LegacyNsfw/52Can/Software/Constants.h

// Color definitions
#define BLACK    0x0000
#define BLUE     0x001F
#define RED      0xF800
#define GREEN    0x07E0
#define CYAN     0x07FF
#define MAGENTA  0xF81F
#define YELLOW   0xFFE0 
#define WHITE    0xFFFF

#define RGB(red,green,blue) (((red & 0xf8)<<8) + ((green & 0xfc)<<3)+(blue>>3))
#define GREY      RGB(0x80, 0x80, 0x80)
#define LIGHTGREY RGB(0x40, 0x40, 0x40)
#define VERYLIGHTGREY RGB(0x20, 0x20, 0x20) // barely visible
#define LIGHTBLUE RGB(0x40, 0x40, 0xFF)

#define width 160
#define height 128

// SPI pin definitions
#define BL   5
#define SCLK 8
#define MOSI 10
#define CS   2
#define DC   3
#define RST  4

// Using AEM's CAN value convention
// .0001 Lambda/bit, so a uint16_t represents 0 to 6.5535 Lambda
#define MAX_LAMBDA ((uint16_t)(10 * 1000 * 1.36)) // 20:1
#define MIN_LAMBDA ((uint16_t)(10 * 1000 * 0.68)) // 10:1

// Define this to use mock data instead of CAN data
#define MOCK_DATA

// Gauge types
// #define GAUGE_DUAL_AFR
// #define GAUGE_DUAL_AFR
#define GAUGE_COMBINATION_ALARM // Fuel pressure, oil temperature, and knock
